iancho-eng/8bit-CPU/pcb/MAR + IR Module/MAR + Instruction Register pcb.kicad_pcb

## KiCad design pcb/MAR + IR Module/MAR + Instruction Register pcb.kicad_pcb (2026-09-13)

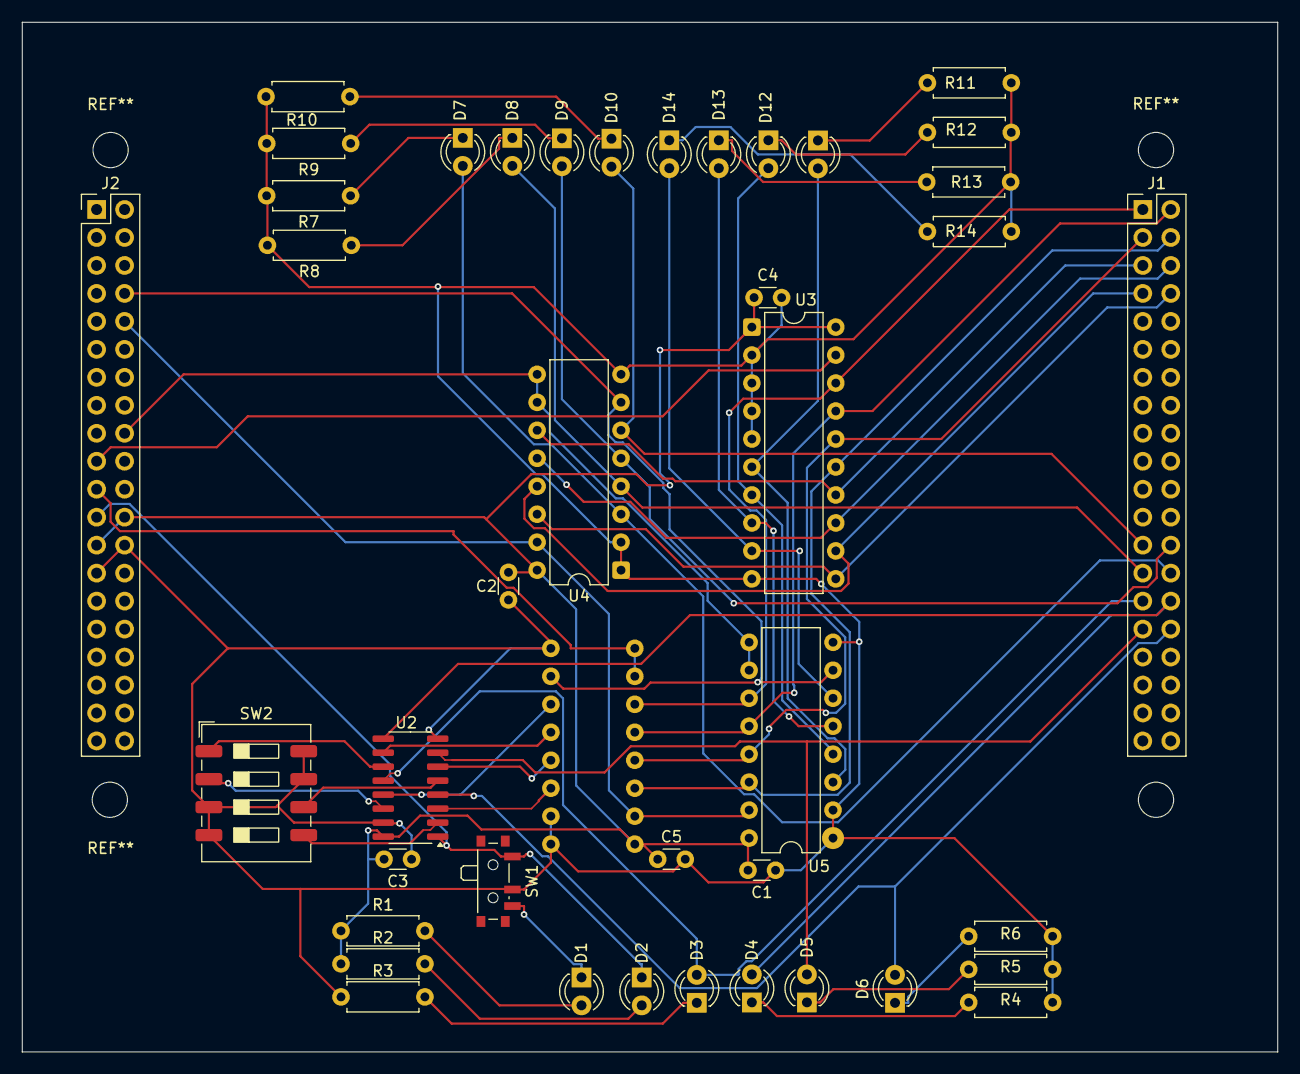
[picture p54: board MAR + Instruction Register pcb.kicad_pcb from above]

Board: 2 copper layers, 114.0 x 93.5 mm, 42 parts (1 on the bottom side), 51 nets.

Parts:
C1, C2, C3, C4, C5: 0.1uF; C_Disc_D3.0mm_W1.6mm_P2.50mm
D1: GREEN; LED_D3.0mm
D2: RED; LED_D3.0mm
D3, D4, D5, D6, D11, D12, D13, D14: YELLOW; LED_D3.0mm
D7, D8, D9, D10: BLUE; LED_D3.0mm
J1, J2: Conn_02x20_Odd_Even; PinHeader_2x20_P2.54mm_Vertical
R1, R2: 1K; R_Axial_DIN0207_L6.3mm_D2.5mm_P7.62mm_Horizontal
R3, R4, R5, R6, R7, R8, R9, R10, R11, R12, R13, R14: 220; R_Axial_DIN0207_L6.3mm_D2.5mm_P7.62mm_Horizontal
SW1: SW_SPDT; SW_SPDT_PCM12
SW2: SW_DIP_x04; SW_DIP_SPSTx04_Slide_9.78x12.34mm_W8.61mm_P2.54mm
U1, U4, U5: 74HCT173; DIP-16_W7.62mm
U2: 74HCT157D; SOIC-16_3.9x9.9mm_P1.27mm
U3: 74HCT245N; DIP-20_W7.62mm

Connections:
/Instruction Register Module/BUS_0: J1.1, U1.11 (D3), U3.18 (B0), U5.11 (D3)
/Instruction Register Module/BUS_1: J1.2, U1.12 (D2), U3.17 (B1), U5.12 (D2)
/Instruction Register Module/BUS_2: J1.3, U1.13 (D1), U3.16 (B2), U5.13 (D1)
/Instruction Register Module/BUS_3: J1.4, U1.14 (D0), U3.15 (B3), U5.14 (D0)
/Instruction Register Module/BUS_4: J1.5, U3.14 (B4), U4.11 (D3)
/Instruction Register Module/BUS_5: J1.6, U3.13 (B5), U4.12 (D2)
/Instruction Register Module/BUS_6: J1.7, U3.12 (B6), U4.13 (D1)
/Instruction Register Module/BUS_7: J1.8, U3.11 (B7), U4.14 (D0)
/Instruction Register Module/CLK: J2.8, U1.7 (Cp), U4.7 (Cp), U5.7 (Cp)
/Instruction Register Module/CLR: J2.10, U1.15 (Mr), U4.15 (Mr), U5.15 (Mr)
/Instruction Register Module/IR_4: D10.2 (A), J1.25, U4.6 (Q3)
/Instruction Register Module/IR_5: D9.2 (A), J1.26, U4.5 (Q2)
/Instruction Register Module/IR_6: D8.2 (A), J1.27, U4.4 (Q1)
/Instruction Register Module/IR_7: D7.2 (A), J1.28, U4.3 (Q0)
/Instruction Register Module/~II: J2.18, U4.9 (E1), U4.10 (E2), U5.9 (E1), U5.10 (E2)
/Instruction Register Module/~IO: J2.19, U3.19 (~OE)
/Memory Address Register Module/A0: D3.2 (A), J1.29, U2.12 (4Y)
/Memory Address Register Module/A1: D4.2 (A), J1.30, U2.9 (3Y)
/Memory Address Register Module/A2: D5.2 (A), J1.31, U2.7 (2Y)
/Memory Address Register Module/A3: D6.2 (A), J1.32, U2.4 (1Y)
/Memory Address Register Module/PROG: D2.1 (K), J2.23, SW1.1 (A), U2.1 (S)
/Memory Address Register Module/~MI: J2.21, U1.9 (E1), U1.10 (E2)
GND: C1.2, C2.2, C3.2, C4.2, C5.2, J2.26, J2.27, R3.1, R4.1, R5.1, R6.1, R7.2, R8.2, R9.2, R10.2, R11.2, R12.2, R13.2, R14.2, SW1.2 (B), SW2.3, SW2.4, SW2.7, SW2.8, U1.1 (Oe1), U1.2 (Oe2), U1.8 (GND), U2.8 (GND), U2.15 (~E), U3.2 (A0), U3.3 (A1), U3.4 (A2), U3.5 (A3), U3.10 (GND), U4.1 (Oe1), U4.2 (Oe2), U4.8 (GND), U5.1 (Oe1), U5.2 (Oe2), U5.8 (GND)
unnamed: D1.2 (A), R1.2
unnamed: D1.1 (K), SW1.3 (C)
unnamed: D2.2 (A), R2.2
unnamed: D3.1 (K), R3.2
unnamed: D4.1 (K), R4.2
unnamed: D5.1 (K), R5.2
unnamed: D6.1 (K), R6.2
unnamed: D7.1 (K), R7.1
unnamed: D8.1 (K), R8.1
unnamed: D9.1 (K), R9.1
unnamed: D10.1 (K), R10.1
unnamed: D11.2 (A), U3.6 (A4), U5.3 (Q0)
unnamed: D11.1 (K), R11.1
unnamed: D12.2 (A), U3.7 (A5), U5.4 (Q1)
unnamed: D12.1 (K), R12.1
unnamed: D13.2 (A), U3.8 (A6), U5.5 (Q2)
unnamed: D13.1 (K), R13.1
unnamed: D14.2 (A), U3.9 (A7), U5.6 (Q3)
unnamed: D14.1 (K), R14.1
unnamed: U1.3 (Q0), U2.3 (1I1)
unnamed: U1.4 (Q1), U2.6 (2I1)
unnamed: U1.5 (Q2), U2.10 (3I1)
unnamed: U1.6 (Q3), U2.13 (4I1)
unnamed: SW2.5, U2.2 (1I0)
unnamed: SW2.6, U2.5 (2I0)
unnamed: SW2.1, U2.11 (3I0)
unnamed: SW2.2, U2.14 (4I0)
VCC: C1.1, C2.1, C3.1, C4.1, C5.1, J2.24, J2.25, R1.1, R2.1, U1.16 (VCC), U2.16 (VCC), U3.1 (DIR), U3.20 (VCC), U4.16 (VCC), U5.16 (VCC)
