iancho-eng/8bit-CPU/pcb/Control Logic Module/ControlLogic_Board.kicad_pcb

## KiCad design pcb/Control Logic Module/ControlLogic_Board.kicad_pcb (2026-09-13)

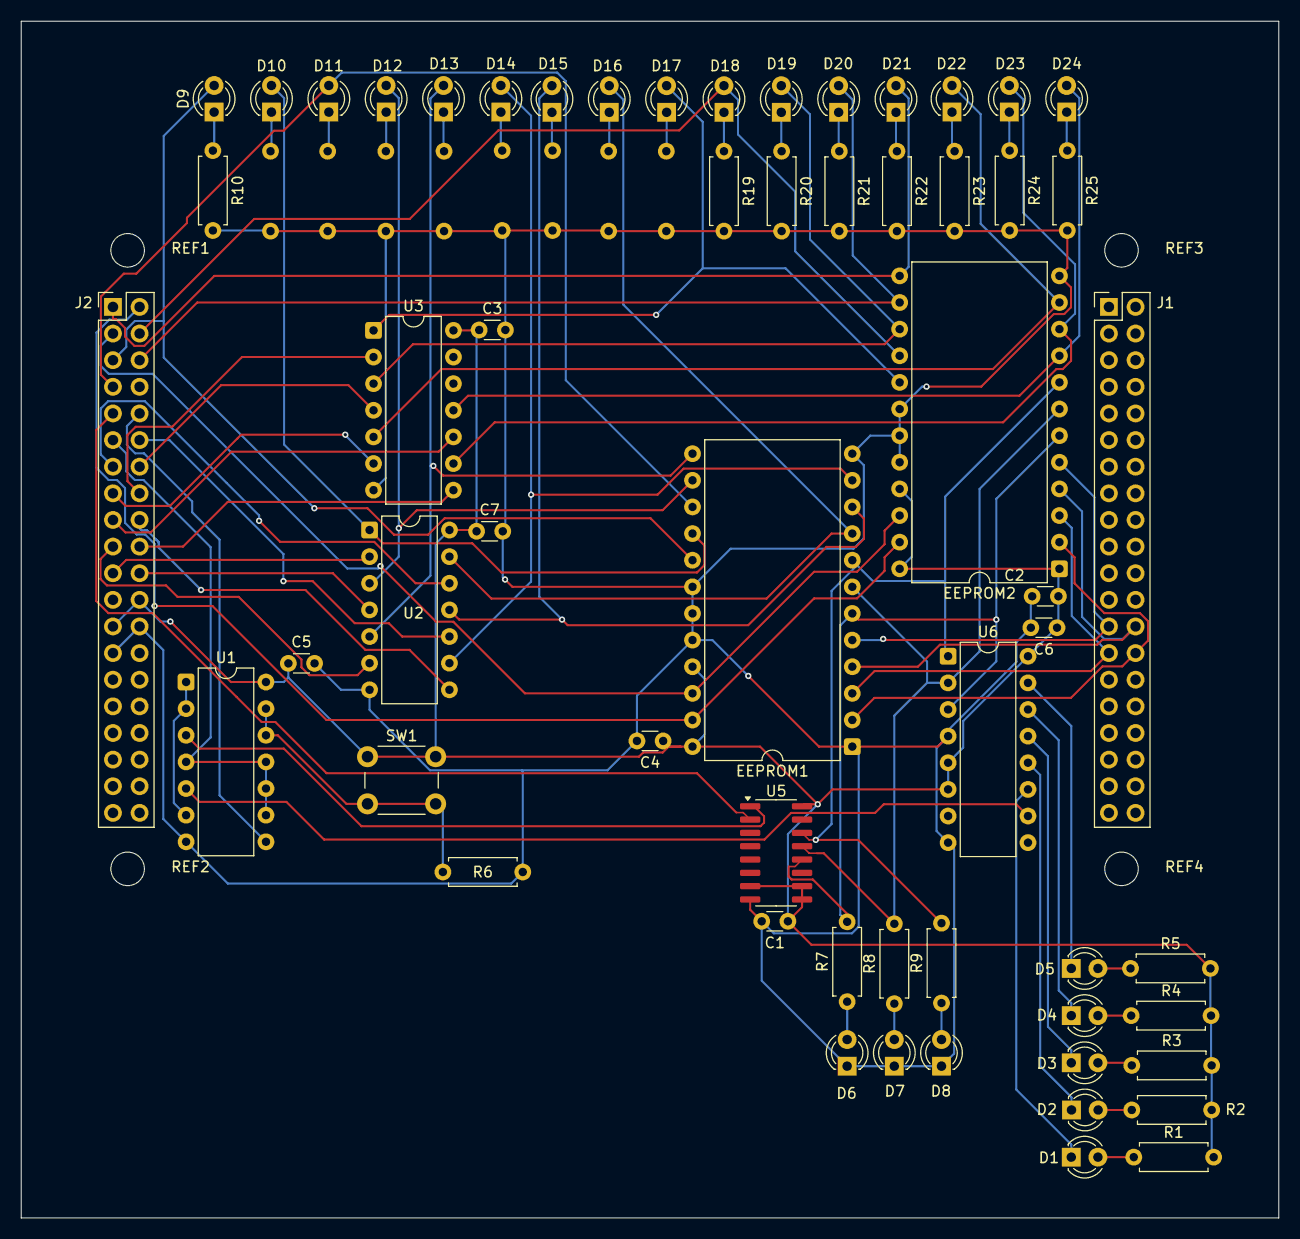
[picture p55: board ControlLogic_Board.kicad_pcb from above]

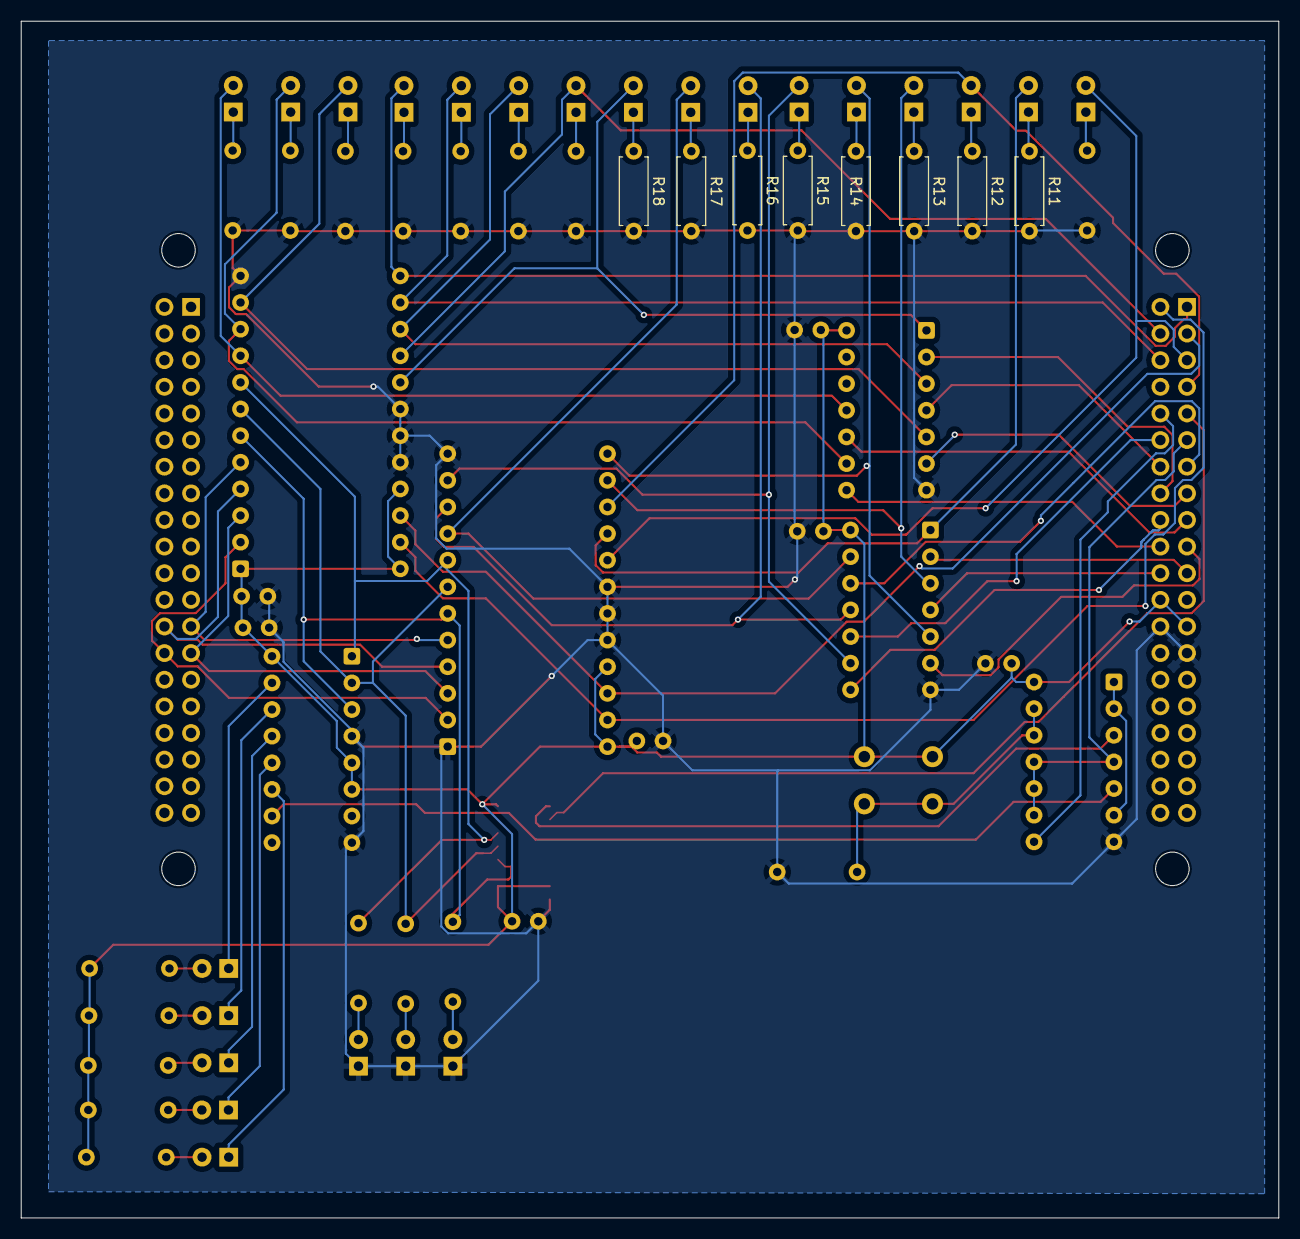
[picture p56: board ControlLogic_Board.kicad_pcb from below]

Board: 2 copper layers, 119.9 x 114.2 mm, 70 parts (8 on the bottom side), 74 nets.

Parts:
C1, C2, C3, C4, C5, C6, C7: 0.1uF; C_Disc_D3.0mm_W1.6mm_P2.50mm
D1, D2, D3, D4, D5: GREEN; LED_D3.0mm
D6, D7, D8: RED; LED_D3.0mm
D9, D10, D11, D12, D13, D14, D15, D16, D17, D18, D19, D20, D21, D22, D23, D24: BLUE; LED_D3.0mm
EEPROM1, EEPROM2: DIP-24_W15.24mm
J1, J2: Conn_02x20_Odd_Even; PinHeader_2x20_P2.54mm_Vertical
R1, R2, R3, R4, R5, R7, R8, R9, R10, R11, R12, R13, R14, R15, R16, R17, R18, R19, R20, R21, R22, R23, R24, R25: 220; R_Axial_DIN0207_L6.3mm_D2.5mm_P7.62mm_Horizontal
R6: 1K; R_Axial_DIN0207_L6.3mm_D2.5mm_P7.62mm_Horizontal
REF1, REF2, REF3, REF4: MountingHole_3.2mm_M3
SW1: SW_Push; SW_PUSH_6mm
U1: 74HCT00; DIP-14_W7.62mm
U2, U3: 74HCT04; DIP-14_W7.62mm
U5: 74HCT161D; SOIC-16_3.9x9.9mm_P1.27mm
U6: 74HCT138; DIP-16_W7.62mm

Connections:
/control logic/CE: D21.2 (A), EEPROM2.13 (D3), J2.1
/control logic/CF: EEPROM1.23 (A8), EEPROM2.23 (A8), J2.2
/control logic/CLR: J2.10, U1.8
/control logic/HLT: D9.2 (A), EEPROM1.17 (D7), J2.5
/control logic/IR_4: EEPROM1.5 (A3), EEPROM2.5 (A3), J1.25
/control logic/IR_5: EEPROM1.4 (A4), EEPROM2.4 (A4), J1.26
/control logic/IR_6: EEPROM1.3 (A5), EEPROM2.3 (A5), J1.27
/control logic/IR_7: EEPROM1.2 (A6), EEPROM2.2 (A6), J1.28
/control logic/OI: D20.2 (A), EEPROM2.14 (D4), J2.6
/control logic/RI: D11.2 (A), EEPROM1.15 (D5), J2.7
/control logic/SU: D18.2 (A), EEPROM2.16 (D6), J2.4
/control logic/ZF: EEPROM1.22 (A9), EEPROM2.22 (A9), J2.3
/control logic/~AI: J2.12, U2.10
/control logic/~AO: J2.13, U2.12
/control logic/~BI: J2.14, U3.4
/control logic/~CLK: J2.9, U5.2 (CP)
/control logic/~CLR: J2.11, U1.4, U1.9, U1.10, U1.11
/control logic/~CO: J2.15, U3.6
/control logic/~EO: J2.16, U3.2
/control logic/~FI: J2.17, U3.10
/control logic/~II: J2.18, U2.8
/control logic/~IO: J2.19, U2.6
/control logic/~J: J2.20, U3.8
/control logic/~MI: J2.21, U2.2
/control logic/~RO: J2.22, U2.4
GND: C1.2, C2.2, C3.2, C4.2, C5.2, C6.2, C7.2, D6.1 (K), D7.1 (K), D8.1 (K), EEPROM1.1 (A7), EEPROM1.12 (GND), EEPROM1.18 (~CE), EEPROM1.19 (A10), EEPROM1.20 (~OE), EEPROM2.12 (GND), EEPROM2.18 (~CE), EEPROM2.19 (A10), EEPROM2.20 (~OE), J2.26, J2.27, R6.2, R10.2, R11.2, R12.2, R13.2, R14.2, R15.2, R16.2, R17.2, R18.2, R19.2, R20.2, R21.2, R22.2, R23.2, R24.2, R25.2, U1.7 (GND), U2.7 (GND), U3.7 (GND), U5.8 (GND), U6.4 (~E0), U6.8 (GND)
unnamed: D1.2 (A), R1.1
unnamed: D1.1 (K), U6.11 (~Y4)
unnamed: D2.2 (A), R2.1
unnamed: D2.1 (K), U6.12 (~Y3)
unnamed: D3.2 (A), R3.1
unnamed: D3.1 (K), U6.13 (~Y2)
unnamed: D4.2 (A), R4.1
unnamed: D4.1 (K), U6.14 (~Y1)
unnamed: D5.2 (A), R5.1
unnamed: D5.1 (K), U6.15 (~Y0)
unnamed: D6.2 (A), R7.1
unnamed: D7.2 (A), R8.1
unnamed: D8.2 (A), R9.1
unnamed: D9.1 (K), R10.1
unnamed: D10.2 (A), EEPROM1.16 (D6), U2.1
unnamed: D10.1 (K), R11.1
unnamed: D11.1 (K), R12.1
unnamed: D12.2 (A), EEPROM1.14 (D4), U2.3
unnamed: D12.1 (K), R13.1
unnamed: D13.2 (A), EEPROM1.13 (D3), U2.5
unnamed: D13.1 (K), R14.1
unnamed: D14.2 (A), EEPROM1.11 (D2), U2.9
unnamed: D14.1 (K), R15.1
unnamed: D15.2 (A), EEPROM1.10 (D1), U2.11
unnamed: D15.1 (K), R16.1
unnamed: D16.2 (A), EEPROM1.9 (D0), U2.13
unnamed: D16.1 (K), R17.1
unnamed: D17.2 (A), EEPROM2.17 (D7), U3.1
unnamed: D17.1 (K), R18.1
unnamed: D18.1 (K), R19.1
unnamed: D19.2 (A), EEPROM2.15 (D5), U3.3
unnamed: D19.1 (K), R20.1
unnamed: D20.1 (K), R21.1
unnamed: D21.1 (K), R22.1
unnamed: D22.2 (A), EEPROM2.11 (D2), U3.5
unnamed: D22.1 (K), R23.1
unnamed: D23.2 (A), EEPROM2.10 (D1), U3.9
unnamed: D23.1 (K), R24.1
unnamed: D24.2 (A), EEPROM2.9 (D0), U3.11
unnamed: D24.1 (K), R25.1
unnamed: EEPROM1.8 (A0), EEPROM2.8 (A0), R9.2, U5.14 (Q0), U6.1 (A0)
unnamed: EEPROM1.7 (A1), EEPROM2.7 (A1), R8.2, U5.13 (Q1), U6.2 (A1)
unnamed: EEPROM1.6 (A2), EEPROM2.6 (A2), R7.2, U5.12 (Q2), U6.3 (A2)
unnamed: R6.1, SW1.2, U1.12, U1.13
unnamed: U1.1, U1.2, U1.6
unnamed: U1.3, U5.1 (~MR)
unnamed: U1.5, U6.10 (~Y5)
VCC: C1.1, C2.1, C3.1, C4.1, C5.1, C6.1, C7.1, EEPROM1.21 (~WE), EEPROM1.24 (VCC), EEPROM2.1 (A7), EEPROM2.21 (~WE), EEPROM2.24 (VCC), J2.24, J2.25, R1.2, R2.2, R3.2, R4.2, R5.2, SW1.1, U1.14 (VCC), U2.14 (VCC), U3.14 (VCC), U5.7 (CEP), U5.9 (~PE), U5.10 (CET), U5.16 (VCC), U6.5 (~E1), U6.6 (E2), U6.16 (VCC)
