iancho-eng/8bit-CPU/pcb/Clock Module/Clock pcb schematic.kicad_pcb

## KiCad design pcb/Clock Module/Clock pcb schematic.kicad_pcb (2026-09-13)

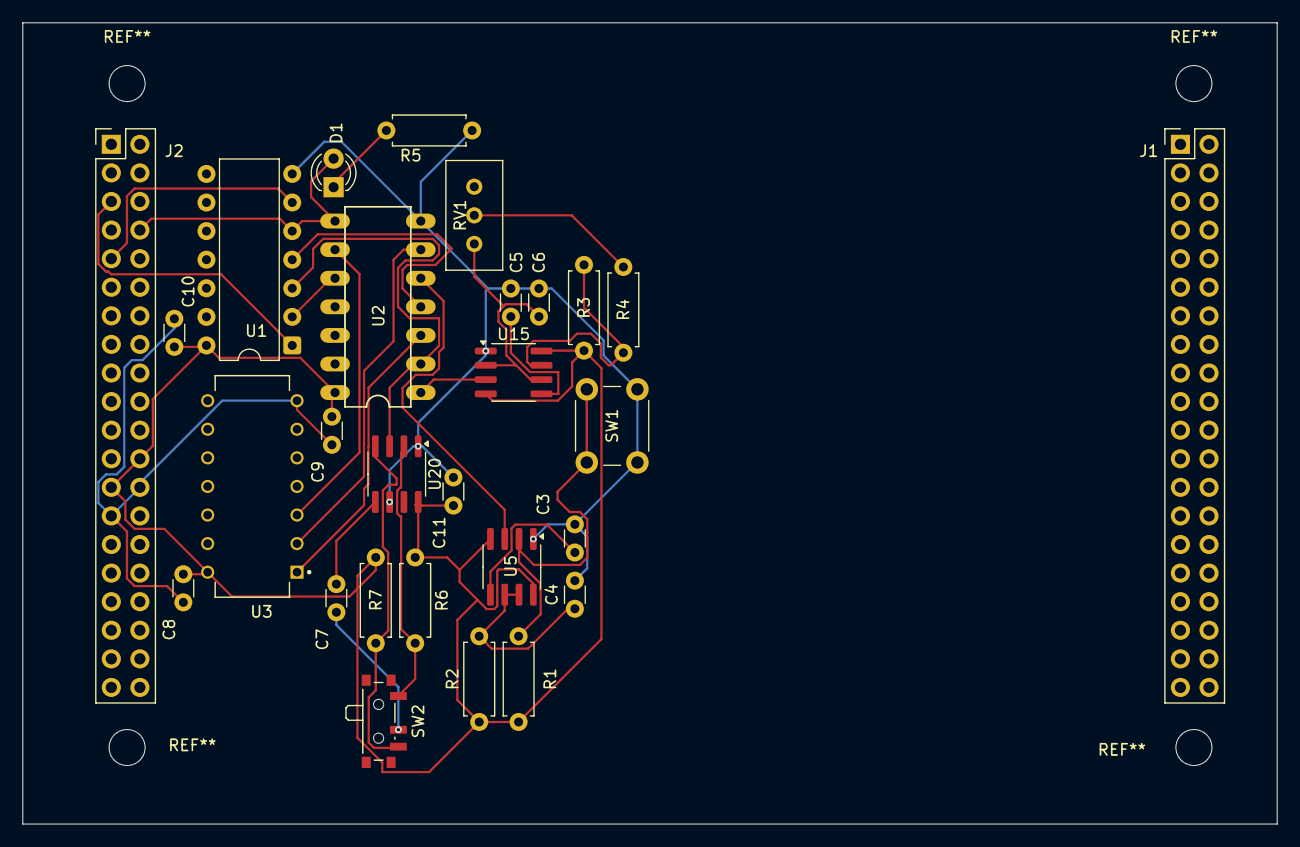
[picture p57: board Clock pcb schematic.kicad_pcb from above]

Board: 2 copper layers, 111.5 x 71.2 mm, 28 parts (0 on the bottom side), 24 nets.

Parts:
C3, C5, C7, C8, C9, C10, C11: 0.01uF; C_Disc_D3.0mm_W1.6mm_P2.50mm
C4: 0.1uF; C_Disc_D3.0mm_W1.6mm_P2.50mm
C6: 1uF; C_Disc_D3.0mm_W1.6mm_P2.50mm
D1: BLUE; LED_D3.0mm
J1, J2: Conn_02x20_Odd_Even; PinHeader_2x20_P2.54mm_Vertical
R1, R3, R4, R6, R7: 1K; R_Axial_DIN0207_L6.3mm_D2.5mm_P7.62mm_Horizontal
R2: 1M; R_Axial_DIN0207_L6.3mm_D2.5mm_P7.62mm_Horizontal
R5: 220; R_Axial_DIN0207_L6.3mm_D2.5mm_P7.62mm_Horizontal
RV1: 1M; Potentiometer_Bourns_3296W_Vertical
SW1: SW_Push; SW_PUSH_6mm
SW2: SW_SPDT; SW_SPDT_PCM12
U1: 74HCT04; DIP-14_W7.62mm
U2: 74LS08
U3: 74LS32; DIP794W45P254L1969H508Q14
U5, U15, U20: LM555xM; SOIC-8_3.9x4.9mm_P1.27mm

Connections:
/Clock Module/CLK: D1.2 (A), J2.8, U1.5, U2.8
/Clock Module/HLT: J2.5, U1.1
/Clock Module/~CLK: J2.9, U1.6
GND: C3.2, C4.2, C5.2, C6.2, C7.2, C8.2, C9.2, C10.2, C11.1, J2.26, J2.27, R5.2, SW1.1, SW2.2 (B), U1.7 (GND), U2.7 (GND), U3.7 (GND), U5.1 (GND), U15.1 (GND), U20.1 (GND), U20.6 (THR)
unnamed: D1.1 (K), R5.1
unnamed: R4.1, RV1.2
unnamed: R6.2, SW2.1 (A), U20.2 (TR)
unnamed: R7.2, SW2.3 (C), U20.4 (R)
unnamed: U1.2, U2.10
unnamed: U1.4, U2.4
unnamed: U2.3, U3.1
unnamed: U2.6, U3.2
unnamed: U2.9, U3.3
unnamed: C3.1, U5.5 (CV)
unnamed: C4.1, R2.2, U5.6 (THR), U5.7 (DIS)
unnamed: U2.5, U5.3 (Q)
unnamed: R1.2, SW1.2, U5.2 (TR)
unnamed: C5.1, U15.5 (CV)
unnamed: R3.2, R4.2, U15.7 (DIS)
unnamed: U2.1, U15.3 (Q)
unnamed: C6.1, RV1.3, U15.2 (TR), U15.6 (THR)
unnamed: C7.1, U20.5 (CV)
unnamed: U1.3, U2.2, U20.3 (Q)
VCC: C8.1, C9.1, C10.1, C11.2, J2.24, J2.25, R1.1, R2.1, R3.1, R6.1, R7.1, U1.14 (VCC), U2.14 (VCC), U3.14 (VCC), U5.4 (R), U5.8 (VCC), U15.4 (R), U15.8 (VCC), U20.8 (VCC)
