iancho-eng/8bit-CPU/pcb/ALU Module/ALU pcb schematic.kicad_pcb

## KiCad design pcb/ALU Module/ALU pcb schematic.kicad_pcb (2026-09-13)

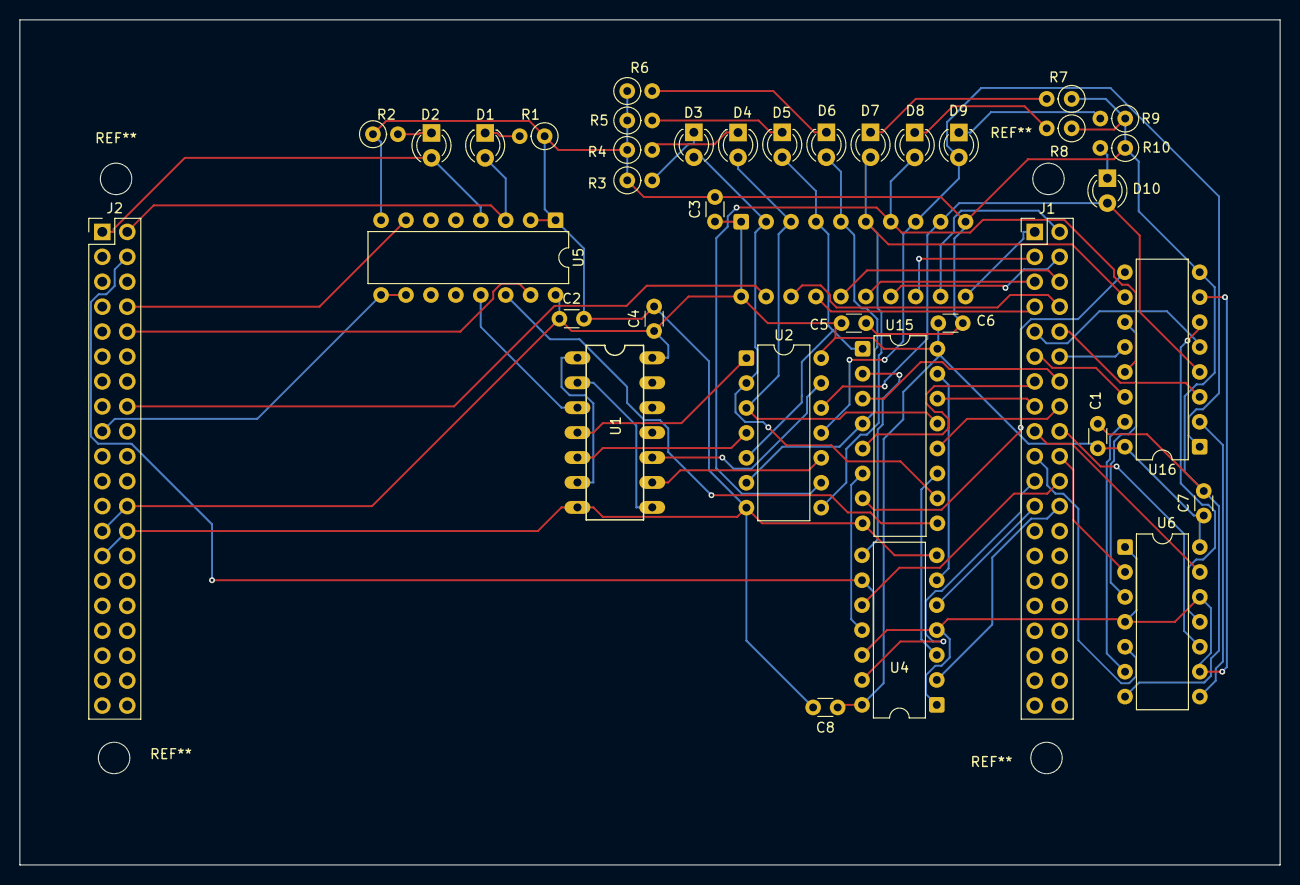
[picture p58: board ALU pcb schematic.kicad_pcb from above]

Board: 2 copper layers, 128.4 x 86.1 mm, 38 parts (1 on the bottom side), 68 nets.

Parts:
C1, C2, C3, C4, C5, C6, C7, C8: 0.1u; C_Disc_D3.0mm_W1.6mm_P2.50mm
D1, D2: LED; LED_D3.0mm
D3, D4, D5, D6, D7, D8, D9, D10: RED; LED_D3.0mm
J1, J2: Conn_02x20_Odd_Even; PinHeader_2x20_P2.54mm_Vertical
R1, R3, R4, R5, R6, R7, R8, R9, R10: 220; R_Axial_DIN0207_L6.3mm_D2.5mm_P2.54mm_Vertical
R2: R; R_Axial_DIN0207_L6.3mm_D2.5mm_P2.54mm_Vertical
U1: 74LS08
U2: 74LS02; DIP-14_W7.62mm
U4, U6: 74LS86; DIP-14_W7.62mm
U5: 74HCT173; DIP-16_W7.62mm
U14: 74HCT245N; DIP-20_W7.62mm
U15, U16: 74LS283; DIP-16_W7.62mm

Connections:
/ALU module/A_0: J1.9, U16.5 (A1)
/ALU module/A_1: J1.10, U16.3 (A2)
/ALU module/A_2: J1.11, U16.14 (A3)
/ALU module/A_3: J1.12, U16.12 (A4)
/ALU module/A_4: J1.13, U15.5 (A1)
/ALU module/A_5: J1.14, U15.3 (A2)
/ALU module/A_6: J1.15, U15.14 (A3)
/ALU module/A_7: J1.16, U15.12 (A4)
/ALU module/BUS_0: J1.1, U14.11 (B7)
/ALU module/BUS_1: J1.2, U14.12 (B6)
/ALU module/BUS_2: J1.3, U14.13 (B5)
/ALU module/BUS_3: J1.4, U14.14 (B4)
/ALU module/BUS_4: J1.5, U14.15 (B3)
/ALU module/BUS_5: J1.6, U14.16 (B2)
/ALU module/BUS_6: J1.7, U14.17 (B1)
/ALU module/BUS_7: J1.8, U14.18 (B0)
/ALU module/B_0: J1.17, U6.13
/ALU module/B_1: J1.18, U6.10
/ALU module/B_2: J1.19, U6.5
/ALU module/B_3: J1.20, U6.2
/ALU module/B_4: J1.21, U4.13
/ALU module/B_5: J1.22, U4.10
/ALU module/B_6: J1.23, U4.5
/ALU module/B_7: J1.24, U4.2
/ALU module/CF: D1.2 (A), J2.2, U5.3 (Q0)
/ALU module/CLK: J2.8, U5.7 (Cp)
/ALU module/CLR: J2.10, U5.15 (Mr)
/ALU module/SU: J2.4, U4.1, U4.4, U4.9, U4.12, U6.1, U6.4, U6.9, U6.12, U16.7 (C0)
/ALU module/ZF: D2.2 (A), J2.1, U5.4 (Q1)
/ALU module/~EO: J2.16, U14.19 (~OE)
/ALU module/~FI: J2.17, U5.9 (E1), U5.10 (E2)
GND: C1.2, C2.2, C3.2, C4.2, C5.2, C6.2, C7.2, C8.2, J2.26, J2.27, R1.1, R2.1, R3.1, R4.1, R5.1, R6.1, R7.1, R8.1, R9.1, R10.1, U1.7 (GND), U2.7 (GND), U4.7 (GND), U5.1 (Oe1), U5.2 (Oe2), U5.8 (GND), U6.7 (GND), U14.10 (GND), U15.8 (GND), U16.8 (GND)
unnamed: D1.1 (K), R1.2
unnamed: D2.1 (K), R2.2
unnamed: D3.2 (A), U2.2, U14.2 (A0), U15.10 (S4)
unnamed: D3.1 (K), R3.2
unnamed: D4.2 (A), U2.3, U14.3 (A1), U15.13 (S3)
unnamed: D4.1 (K), R4.2
unnamed: D5.2 (A), U2.5, U14.4 (A2), U15.1 (S2)
unnamed: D5.1 (K), R5.2
unnamed: D6.2 (A), U2.6, U14.5 (A3), U15.4 (S1)
unnamed: D6.1 (K), R6.2
unnamed: D7.2 (A), U2.8, U14.6 (A4), U16.10 (S4)
unnamed: D7.1 (K), R7.2
unnamed: D8.2 (A), U2.9, U14.7 (A5), U16.13 (S3)
unnamed: D8.1 (K), R8.2
unnamed: D9.2 (A), U2.11, U14.8 (A6), U16.1 (S2)
unnamed: D9.1 (K), R9.2
unnamed: D10.2 (A), U2.12, U14.9 (A7), U16.4 (S1)
unnamed: D10.1 (K), R10.2
unnamed: U1.1, U1.6
unnamed: U1.2, U1.8
unnamed: U1.4, U2.1
unnamed: U1.5, U2.4
unnamed: U1.9, U2.10
unnamed: U1.10, U2.13
unnamed: U1.3, U5.13 (D1)
unnamed: U4.11, U15.6 (B1)
unnamed: U4.8, U15.2 (B2)
unnamed: U4.6, U15.15 (B3)
unnamed: U4.3, U15.11 (B4)
unnamed: U15.7 (C0), U16.9 (C4)
unnamed: U5.14 (D0), U15.9 (C4)
unnamed: U6.11, U16.6 (B1)
unnamed: U6.8, U16.2 (B2)
unnamed: U6.6, U16.15 (B3)
unnamed: U6.3, U16.11 (B4)
VCC: C1.1, C2.1, C3.1, C4.1, C5.1, C6.1, C7.1, C8.1, J2.24, J2.25, U1.14 (VCC), U2.14 (VCC), U4.14 (VCC), U5.16 (VCC), U6.14 (VCC), U14.1 (DIR), U14.20 (VCC), U15.16 (VCC), U16.16 (VCC)
