iancho-eng/8bit-CPU/pcb/Register B Module/Register B pcb schematic.kicad_pcb

## KiCad design pcb/Register B Module/Register B pcb schematic.kicad_pcb (2026-09-13)

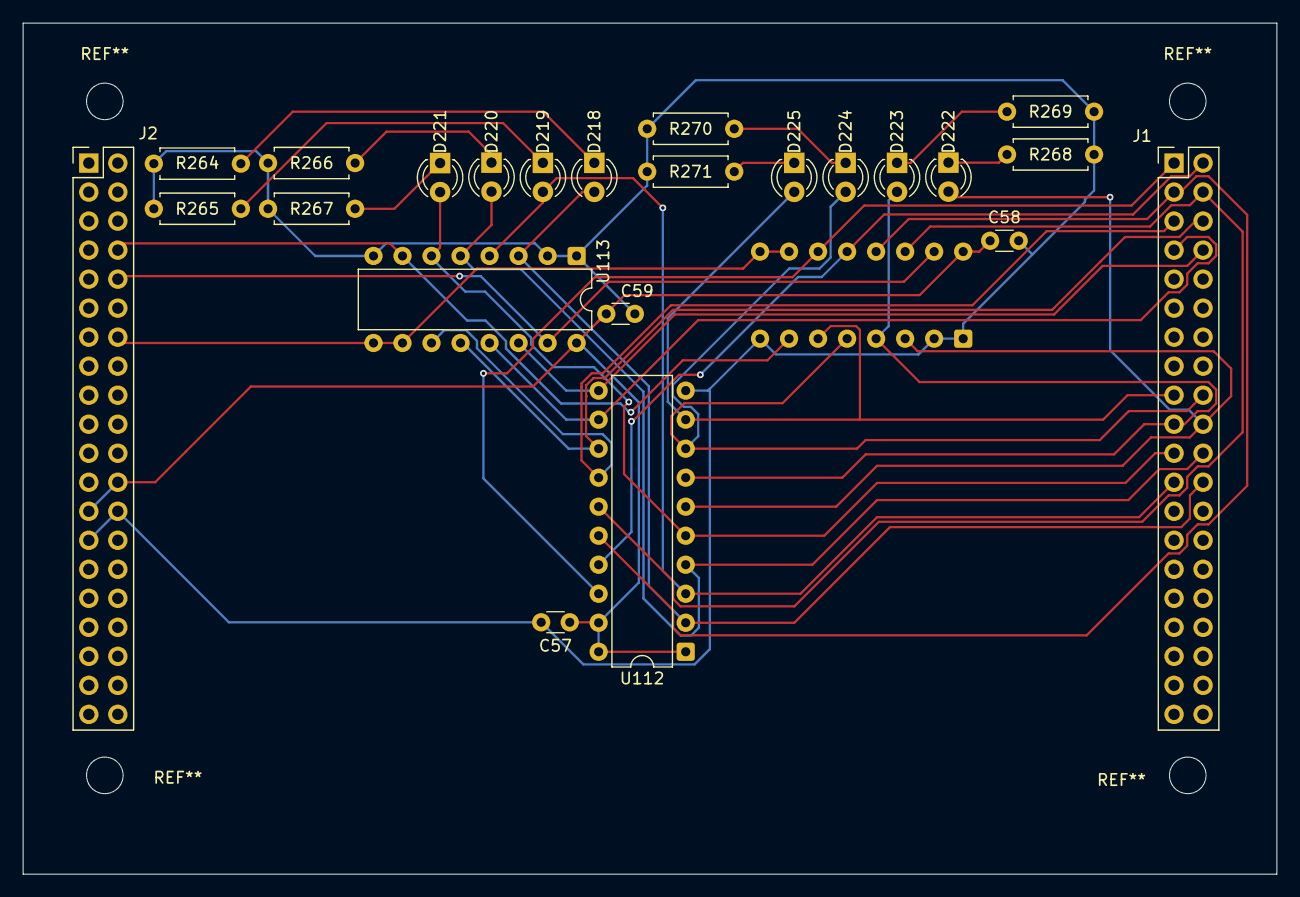
[picture p59: board Register B pcb schematic.kicad_pcb from above]

Board: 2 copper layers, 109.8 x 74.5 mm, 24 parts (1 on the bottom side), 29 nets.

Parts:
C57, C58, C59: 0.1uF; C_Disc_D3.0mm_W1.6mm_P2.50mm
D218, D219, D220, D221, D222, D223, D224, D225: RED; LED_D3.0mm
J1, J2: Conn_02x20_Odd_Even; PinHeader_2x20_P2.54mm_Vertical
R264, R265, R266, R267, R268, R269, R270, R271: 220; R_Axial_DIN0207_L6.3mm_D2.5mm_P7.62mm_Horizontal
U112: 74HCT245N; DIP-20_W7.62mm
U113, U114: 74HCT173; DIP-16_W7.62mm

Connections:
/Register B Module/BUS_0: J1.1, U112.18 (B0), U114.11 (D3)
/Register B Module/BUS_1: J1.2, U112.17 (B1), U114.12 (D2)
/Register B Module/BUS_2: J1.3, U112.16 (B2), U114.13 (D1)
/Register B Module/BUS_3: J1.4, U112.15 (B3), U114.14 (D0)
/Register B Module/BUS_4: J1.5, U112.14 (B4), U113.11 (D3)
/Register B Module/BUS_5: J1.6, U112.13 (B5), U113.12 (D2)
/Register B Module/BUS_6: J1.7, U112.12 (B6), U113.13 (D1)
/Register B Module/BUS_7: J1.8, U112.11 (B7), U113.14 (D0)
/Register B Module/B_0: D225.2 (A), J1.17, U112.9 (A7), U114.6 (Q3)
/Register B Module/B_1: D224.2 (A), J1.18, U112.8 (A6), U114.5 (Q2)
/Register B Module/B_2: D223.2 (A), J1.19, U112.7 (A5), U114.4 (Q1)
/Register B Module/B_3: D222.2 (A), J1.20, U112.6 (A4), U114.3 (Q0)
/Register B Module/B_4: D221.2 (A), J1.21, U112.5 (A3), U113.6 (Q3)
/Register B Module/B_5: D220.2 (A), J1.22, U112.4 (A2), U113.5 (Q2)
/Register B Module/B_6: D219.2 (A), J1.23, U112.3 (A1), U113.4 (Q1)
/Register B Module/B_7: D218.2 (A), J1.24, U112.2 (A0), U113.3 (Q0)
/Register B Module/CLK: J2.8, U113.7 (Cp), U114.7 (Cp)
/Register B Module/CLR: J2.10, U113.15 (Mr), U114.15 (Mr)
/Register B Module/~BI: J2.14, U113.9 (E1), U113.10 (E2), U114.9 (E1), U114.10 (E2)
GND: C57.2, C58.2, C59.2, J2.26, J2.27, R264.2, R265.2, R266.2, R267.2, R268.2, R269.2, R270.2, R271.2, U112.10 (GND), U113.1 (Oe1), U113.2 (Oe2), U113.8 (GND), U114.1 (Oe1), U114.2 (Oe2), U114.8 (GND)
unnamed: D218.1 (K), R264.1
unnamed: D219.1 (K), R265.1
unnamed: D220.1 (K), R266.1
unnamed: D221.1 (K), R267.1
unnamed: D222.1 (K), R268.1
unnamed: D223.1 (K), R269.1
unnamed: D224.1 (K), R270.1
unnamed: D225.1 (K), R271.1
VCC: C57.1, C58.1, C59.1, J2.24, J2.25, U112.1 (DIR), U112.19 (~OE), U112.20 (VCC), U113.16 (VCC), U114.16 (VCC)
