iancho-eng/8bit-CPU/pcb/RAM Module/RAM pcb schematic.kicad_pcb

## KiCad design pcb/RAM Module/RAM pcb schematic.kicad_pcb (2026-09-13)

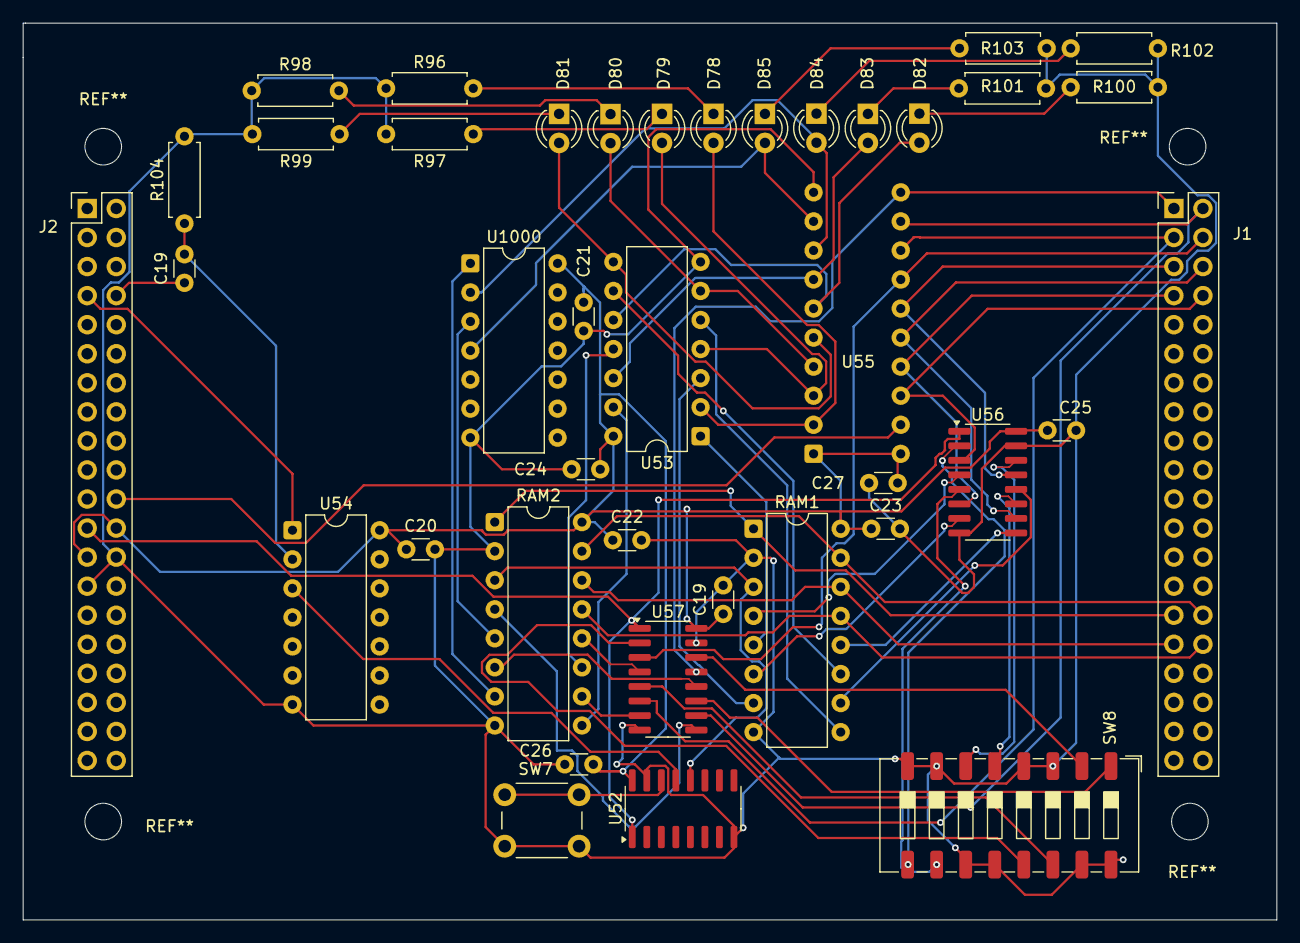
[picture p60: board RAM pcb schematic.kicad_pcb from above]

Board: 2 copper layers, 109.6 x 78.4 mm, 40 parts (1 on the bottom side), 62 nets.

Parts:
C19, C19#2, C20, C21, C22, C23, C24, C25, C26, C27: 0.01uF; C_Disc_D3.0mm_W1.6mm_P2.50mm
D78, D79, D80, D81, D82, D83, D84, D85: RED; LED_D3.0mm
J1, J2: Conn_02x20_Odd_Even; PinHeader_2x20_P2.54mm_Vertical
R96, R97, R98, R99, R100, R101, R102, R103: 220; R_Axial_DIN0207_L6.3mm_D2.5mm_P7.62mm_Horizontal
R104: 1K; R_Axial_DIN0207_L6.3mm_D2.5mm_P7.62mm_Horizontal
RAM1, RAM2: DIP-16_W7.62mm
SW7: SW_Push; SW_PUSH_6mm
SW8: SW_DIP_x08; SW_DIP_SPSTx08_Slide_9.78x22.5mm_W8.61mm_P2.54mm
U52, U56, U57: 74HCT157D; SOIC-16_3.9x9.9mm_P1.27mm
U53, U1000: 74HCT04; DIP-14_W7.62mm
U54: 7400; DIP-14_W7.62mm
U55: 74HCT245N; DIP-20_W7.62mm

Connections:
/RAM/A0: J1.29, RAM1.1 (A₀), RAM2.1 (A₀)
/RAM/A1: J1.30, RAM1.15 (A₁), RAM2.15 (A₁)
/RAM/A2: J1.31, RAM1.14 (A₂), RAM2.14 (A₂)
/RAM/A3: J1.32, RAM1.13 (A₃), RAM2.13 (A₃)
/RAM/BUS_0: J1.1, U55.11 (B7), U57.13 (4I1)
/RAM/BUS_1: J1.2, U55.12 (B6), U57.10 (3I1)
/RAM/BUS_2: J1.3, U55.13 (B5), U57.6 (2I1)
/RAM/BUS_3: J1.4, U55.14 (B4), U57.3 (1I1)
/RAM/BUS_4: J1.5, U55.15 (B3), U56.13 (4I1)
/RAM/BUS_5: J1.6, U55.16 (B2), U56.10 (3I1)
/RAM/BUS_6: J1.7, U55.17 (B1), U56.6 (2I1)
/RAM/BUS_7: J1.8, U55.18 (B0), U56.3 (1I1)
/RAM/CLK: C19#2.1, J2.8
/RAM/PROG: J2.23, U52.1 (S), U56.1 (S), U57.1 (S)
/RAM/RI: J2.7, U54.1
/RAM/~RO: J2.22, U55.19 (~OE)
GND: C19.2, C20.2, C21.2, C22.2, C23.2, C24.1, C25.2, C26.1, C27.1, J2.26, J2.27, R96.2, R97.2, R98.2, R99.2, R100.2, R101.2, R102.2, R103.2, R104.2, RAM1.2 (~CS), RAM1.8 (GND), RAM2.2 (~CS), RAM2.8 (GND), SW7.2, SW8.3, SW8.4, SW8.7, SW8.8, SW8.11, SW8.12, SW8.15, SW8.16, U52.8 (GND), U52.15 (~E), U53.7 (GND), U54.7 (GND), U55.10 (GND), U56.8 (GND), U56.15 (~E), U57.8 (GND), U57.15 (~E), U1000.7 (GND)
unnamed: C19#2.2, R104.1, U54.2
unnamed: D78.2 (A), U53.2, U55.2 (A0)
unnamed: D78.1 (K), R96.1
unnamed: D79.2 (A), U53.4, U55.3 (A1)
unnamed: D79.1 (K), R97.1
unnamed: D80.2 (A), U53.6, U55.4 (A2)
unnamed: D80.1 (K), R98.1
unnamed: D81.2 (A), U53.8, U55.5 (A3)
unnamed: D81.1 (K), R99.1
unnamed: D82.2 (A), U53.10, U55.6 (A4)
unnamed: D82.1 (K), R100.1
unnamed: D83.2 (A), U53.12, U55.7 (A5)
unnamed: D83.1 (K), R101.1
unnamed: D84.2 (A), U55.8 (A6), U1000.2
unnamed: D84.1 (K), R102.1
unnamed: D85.2 (A), U55.9 (A7), U1000.4
unnamed: D85.1 (K), R103.1
unnamed: RAM1.4 (D₀), U56.4 (1Y)
unnamed: RAM1.6 (D₁), U56.7 (2Y)
unnamed: RAM1.10 (D₂), U56.12 (4Y)
unnamed: RAM1.12 (D₃), U56.9 (3Y)
unnamed: RAM1.5 (~O₀), U53.1
unnamed: RAM1.7 (~O₁), U53.3
unnamed: RAM1.9 (~O₂), U53.5
unnamed: RAM1.11 (~O₃), U53.9
unnamed: RAM1.3 (~WE), RAM2.3 (~WE), U52.12 (4Y)
unnamed: RAM2.4 (D₀), U57.9 (3Y)
unnamed: RAM2.6 (D₁), U57.12 (4Y)
unnamed: RAM2.10 (D₂), U57.7 (2Y)
unnamed: RAM2.12 (D₃), U57.4 (1Y)
unnamed: RAM2.5 (~O₀), U1000.3
unnamed: RAM2.7 (~O₁), U1000.1
unnamed: RAM2.9 (~O₂), U53.13
unnamed: RAM2.11 (~O₃), U53.11
unnamed: SW7.1, U52.14 (4I0)
unnamed: U52.13 (4I1), U54.3
unnamed: SW8.9, U56.2 (1I0)
unnamed: SW8.10, U56.5 (2I0)
unnamed: SW8.5, U56.11 (3I0)
unnamed: SW8.6, U56.14 (4I0)
unnamed: SW8.13, U57.2 (1I0)
unnamed: SW8.14, U57.5 (2I0)
unnamed: SW8.1, U57.11 (3I0)
unnamed: SW8.2, U57.14 (4I0)
VCC: C19.1, C20.1, C21.1, C22.1, C23.1, C24.2, C25.1, C26.2, C27.2, J2.24, J2.25, RAM1.16 (Vcc), RAM2.16 (Vcc), U52.16 (VCC), U53.14 (VCC), U54.14 (VCC), U55.1 (DIR), U55.20 (VCC), U56.16 (VCC), U57.16 (VCC), U1000.14 (VCC)
